horizon-blue/dactyl-keyboard/src/parts/hotswap_ridged_test.step

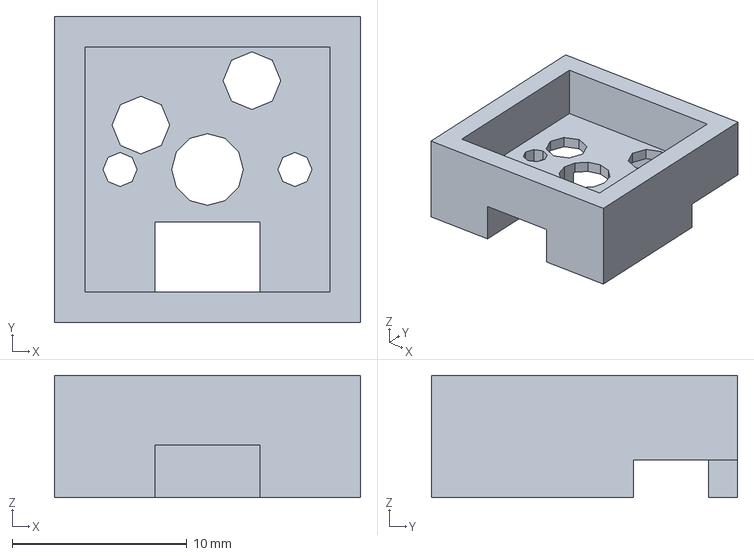
[picture p17: CAD file, 2022-04-09]
src/parts/hotswap_ridged_test.step
17.5 x 17.5 x 7.00 mm
