horizon-blue/dactyl-keyboard/src/parts/trackball_socket_btu.step

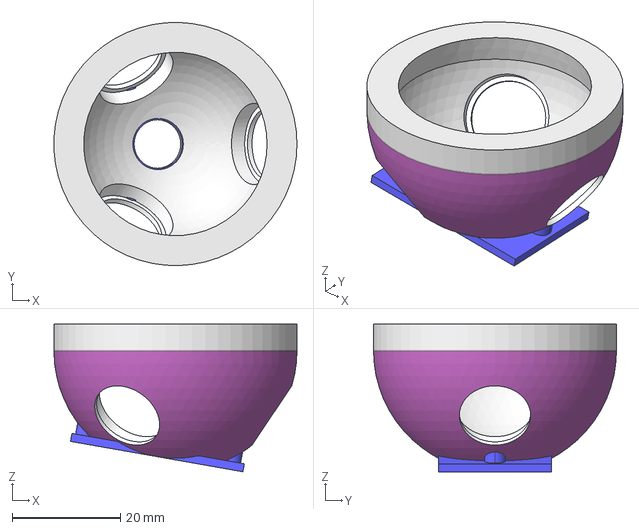
[picture p18: CAD file, 2022-02-23]
src/parts/trackball_socket_btu.step
45.0 x 45.0 x 27.3 mm
