horizon-blue/dactyl-keyboard/src/parts/hotswap_with_ridge.step

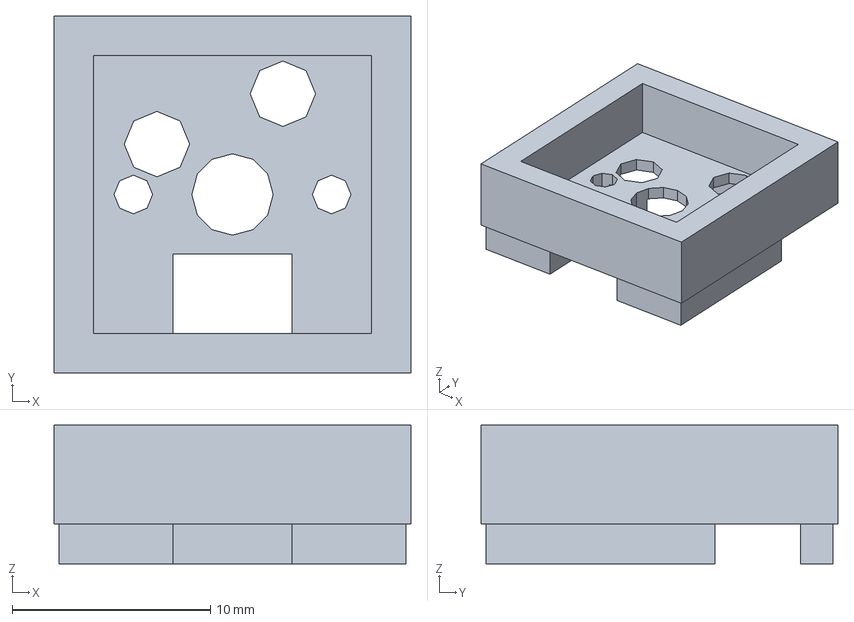
[picture p19: CAD file, 2022-02-22]
src/parts/hotswap_with_ridge.step
18.0 x 18.0 x 7.00 mm
